phastmike/cacophonator/kicad/outputs/v1/images/box_jsl_1.jpg

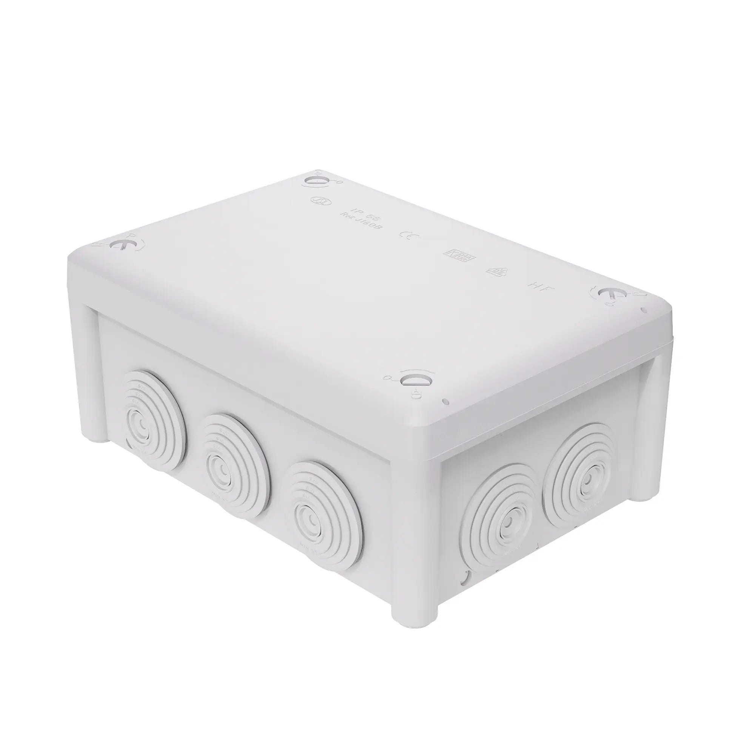
kicad/outputs/v1/images/box_jsl_1.jpg
