phastmike/cacophonator/kicad/outputs/v1/render/cacophonator_bottom.png

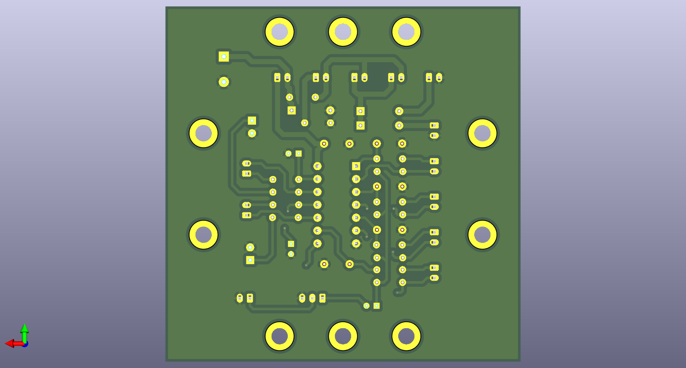
kicad/outputs/v1/render/cacophonator_bottom.png
