phastmike/cacophonator/kicad/outputs/v1/render/cacophonator_top_3d.png

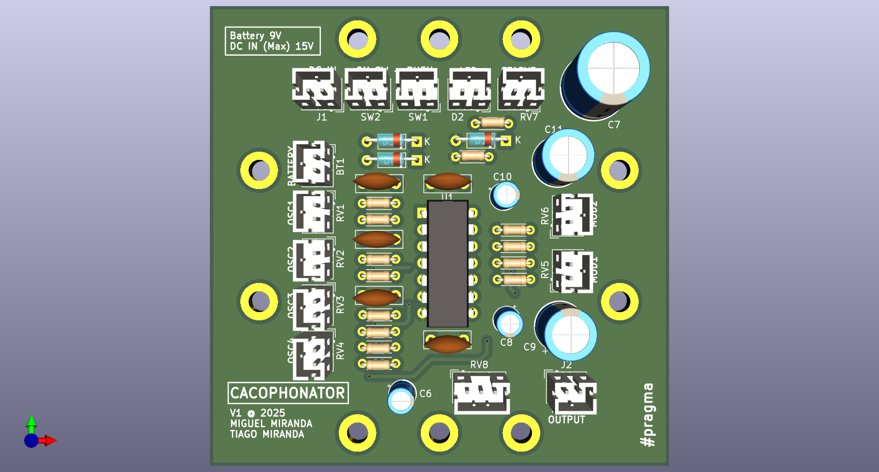
kicad/outputs/v1/render/cacophonator_top_3d.png
